matztam/raymarine-evo-pilot-remote/Schematic/Autopilot_remote_receiver.sch

## EAGLE design Schematic/Autopilot_remote_receiver.sch (2023-01-24)

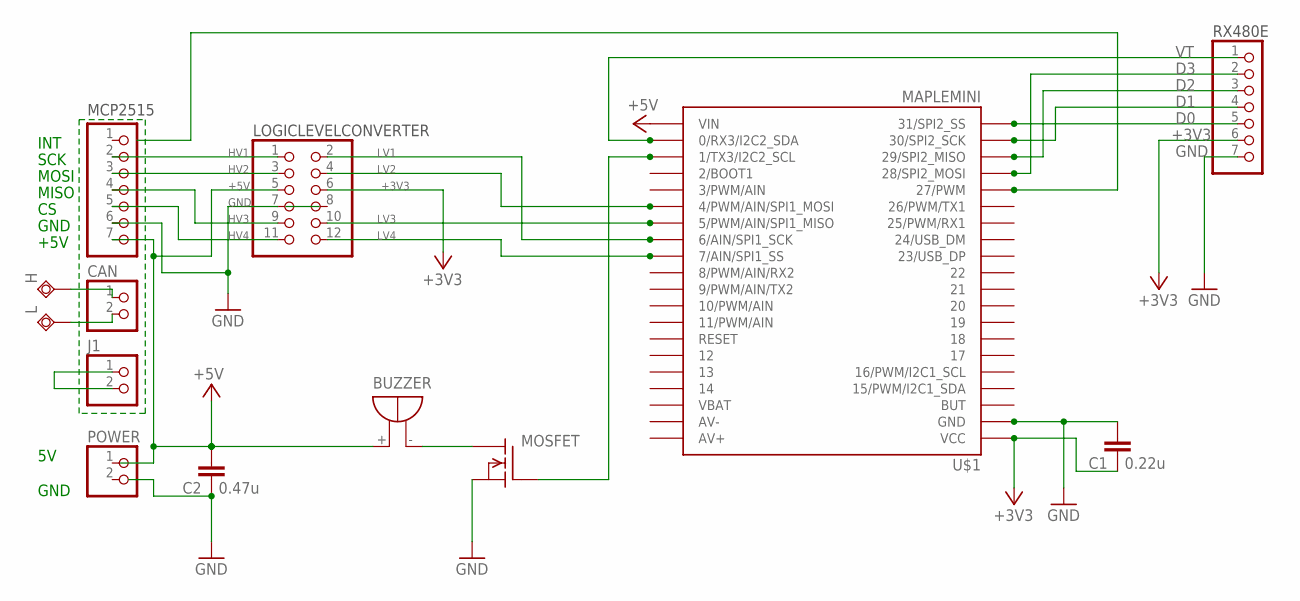
[picture p25: schematic Autopilot_remote_receiver.sch]

Parts:
BUZZER: F/BC35
C1: 0.22u; C050-025X075
C2: 0.47u; C050-025X075
CAN: PINHD-1X2; 1X02
H: TPSQPAD1-20; P1-20
J1: PINHD-1X2; 1X02
L: TPSQPAD1-20; P1-20
LOGICLEVELCONVERTER: PINHD-2X6; 2X06
MCP2515: PINHD-1X7; 1X07
MOSFET: BUZ11; TO220
POWER: PINHD-1X2; 1X02
RX480E: PINHD-1X7; 1X07
U$1: MAPLEMINI; 20-DIP

Connections:
+3V3: C1.1, LOGICLEVELCONVERTER.6, RX480E.6, U$1.1 (VCC)
+5V: BUZZER.+, C2.2, LOGICLEVELCONVERTER.5, MCP2515.7, U$1.21 (VIN)
D0: RX480E.5, U$1.20 (31/SPI2_SS)
D1: RX480E.4, U$1.19 (30/SPI2_SCK)
D2: RX480E.3, U$1.18 (29/SPI2_MISO)
D3: RX480E.2, U$1.17 (28/SPI2_MOSI)
GND: C1.2, C2.1, LOGICLEVELCONVERTER.7, MCP2515.6, MOSFET.3 (S), RX480E.7, U$1.2 (GND)
HV1: LOGICLEVELCONVERTER.1, MCP2515.2
HV2: LOGICLEVELCONVERTER.3, MCP2515.3
HV3: LOGICLEVELCONVERTER.9, MCP2515.4
HV4: LOGICLEVELCONVERTER.11, MCP2515.5
LV1: LOGICLEVELCONVERTER.2, U$1.28 (6/AIN/SPI1_SCK)
LV2: LOGICLEVELCONVERTER.4, U$1.26 (4/PWM/AIN/SPI1_MOSI)
LV3: LOGICLEVELCONVERTER.10, U$1.27 (5/PWM/AIN/SPI1_MISO)
LV4: LOGICLEVELCONVERTER.12, U$1.29 (7/AIN/SPI1_SS)
unnamed: CAN.1, H.TP
unnamed: CAN.2, L.TP
unnamed: J1.1, J1.2
unnamed: BUZZER.-, MOSFET.2 (D)
unnamed: MOSFET.1 (G), U$1.23 (1/TX3/I2C2_SCL)
VT: RX480E.1, U$1.22 (0/RX3/I2C2_SDA)

Notes on the sheet:
+5V
GND
MISO
MOSI
SCK
INT
5V GND
