matztam/raymarine-evo-pilot-remote/Schematic/Autopilot_remote_sender.sch

## EAGLE design Schematic/Autopilot_remote_sender.sch (2023-01-24)

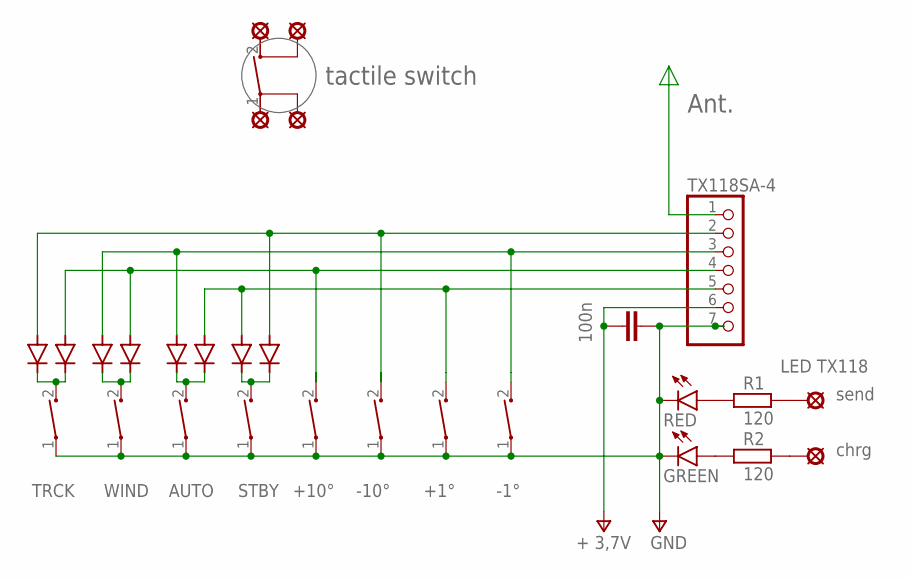
[picture p26: schematic Autopilot_remote_sender.sch]

Parts:
+1°, +10°: CT10-XXXX-A2
-1°, -1°1, -10°: CT10-XXXX-A2
AUTO: CT10-XXXX-A2
C2: 100n; C0805
D5, D6, D7, D8, D9, D10, D11, D12: 1N4148DO35-7; DO35-7
GREEN: LAW51M; W51
LSP1, LSP2, LSP3, LSP4, LSP5, LSP6: LSP10
R1, R2: 120; R0805
RED: LAW51M; W51
STBY: CT10-XXXX-A2
TRCK: CT10-XXXX-A2
TX118SA-4: PINHD-1X7; 1X07
WIND: CT10-XXXX-A2

Connections:
unnamed: +1°.1, +10°.1, -1°.1, -10°.1, AUTO.1, C2.2, GREEN.C, RED.C, STBY.1, TRCK.1, TX118SA-4.7, WIND.1
unnamed: D11.C, D12.C, TRCK.2
unnamed: D9.C, D10.C, WIND.2
unnamed: AUTO.2, D7.C, D8.C
unnamed: D5.C, D6.C, STBY.2
unnamed: +10°.2, D9.A, D11.A, TX118SA-4.4
unnamed: -10°.2, D5.A, D12.A, TX118SA-4.2
unnamed: +1°.2, D6.A, D7.A, TX118SA-4.5
unnamed: -1°.2, D8.A, D10.A, TX118SA-4.3
unnamed: LSP5.MP, R1.2
unnamed: R1.1, RED.A
unnamed: LSP6.MP, R2.2
unnamed: GREEN.A, R2.1
V+: C2.1, TX118SA-4.6

Notes on the sheet:
Ant.
GND
+ 3,7V
LED TX118
send
chrg
tactile switch
